qlab-utwente/Quantum-Dice-by-UTwente/images/bootAndReset.png

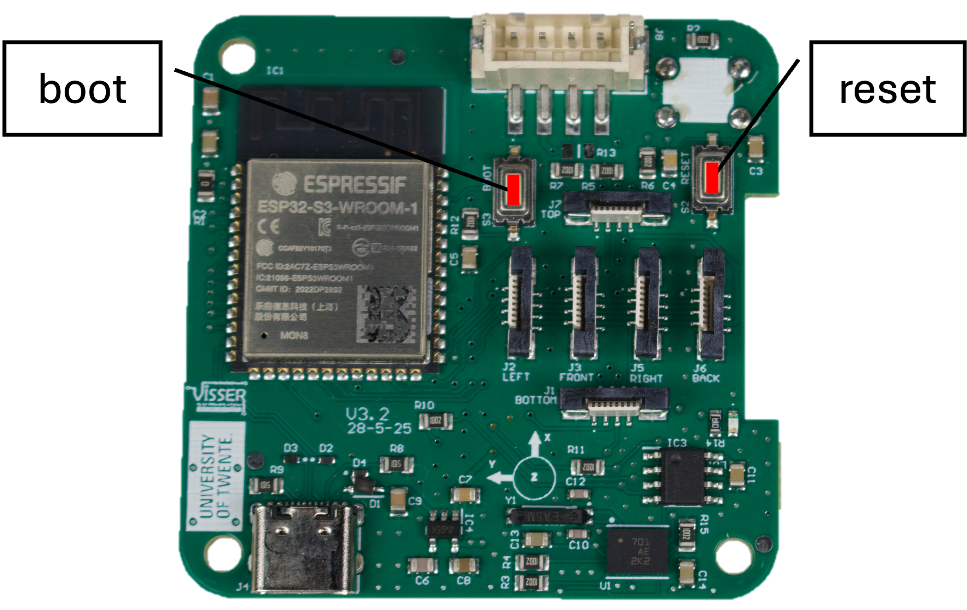
images/bootAndReset.png
