qlab-utwente/Quantum-Dice-by-UTwente/images/ESP32-S3 n16r8 arduino settings.png

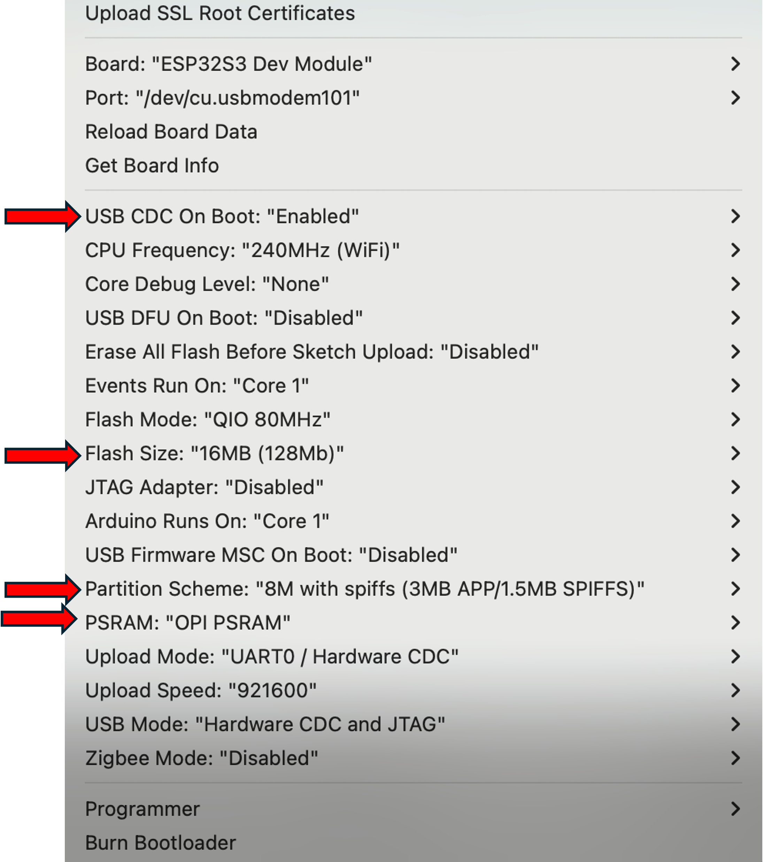
images/ESP32-S3 n16r8 arduino settings.png
