qlab-utwente/Quantum-Dice-by-UTwente/images/Exploded view Quantum Dice 2.png

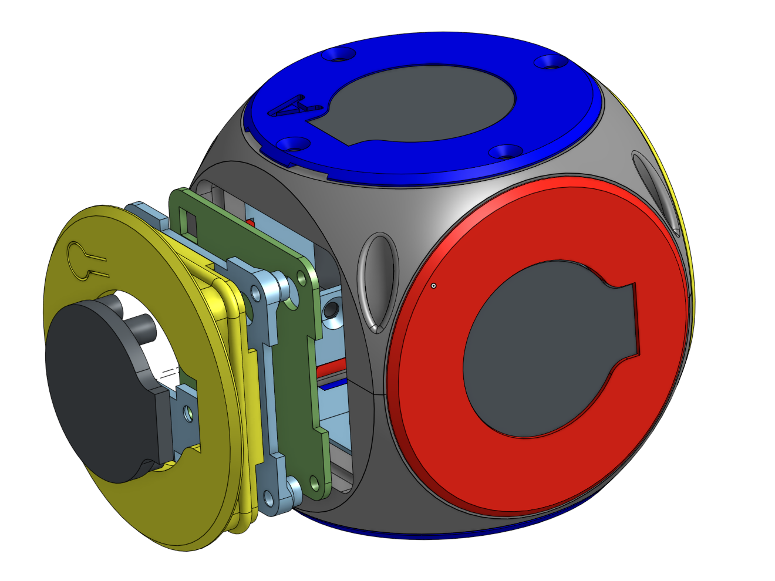
images/Exploded view Quantum Dice 2.png
