qlab-utwente/Quantum-Dice-by-UTwente/images/exploded view quantum dice.png

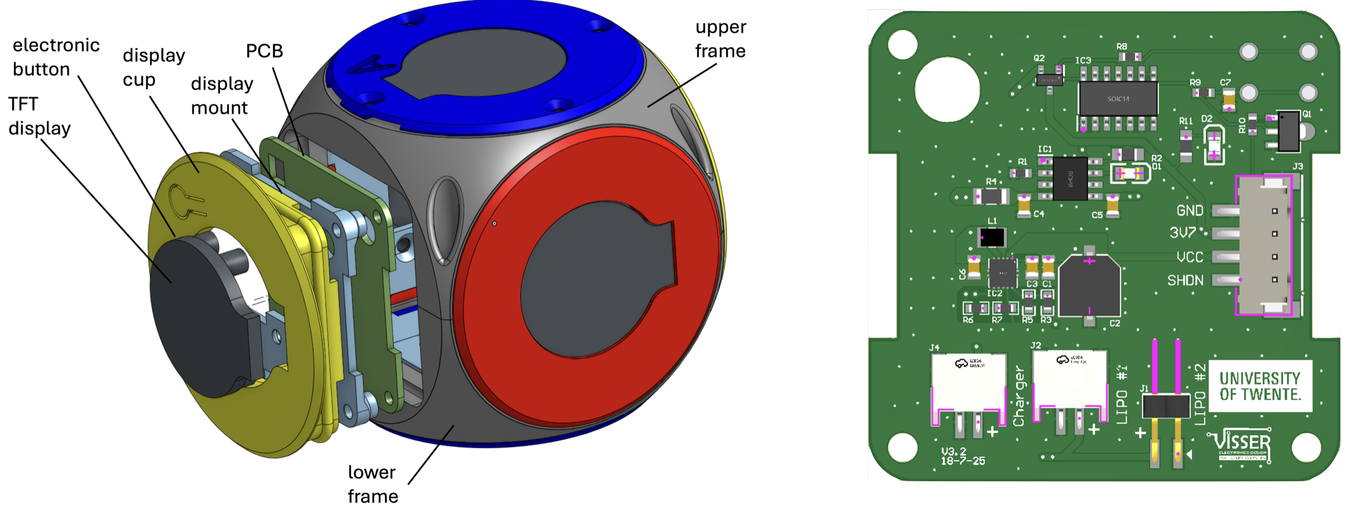
images/exploded view quantum dice.png
