qlab-utwente/Quantum-Dice-by-UTwente/images/FPC slide lock.jpg

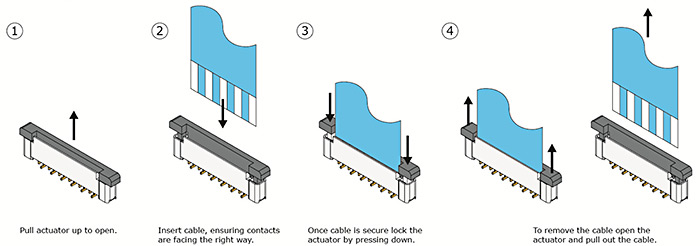
images/FPC slide lock.jpg
