qlab-utwente/Quantum-Dice-by-UTwente/images/Quantum Dice Working Principle.png

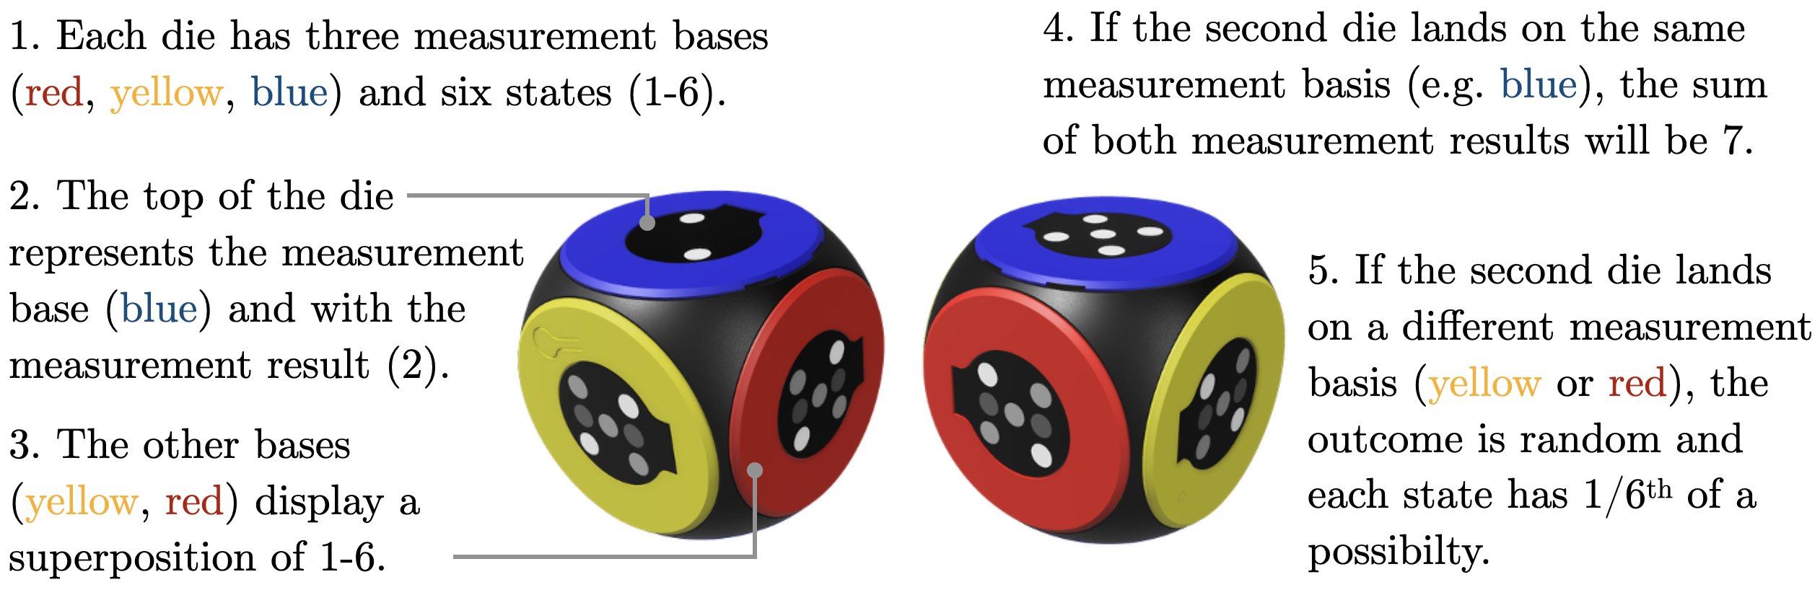
images/Quantum Dice Working Principle.png
