qlab-utwente/Quantum-Dice-by-UTwente/images/single-die-classic-to-superposition.png

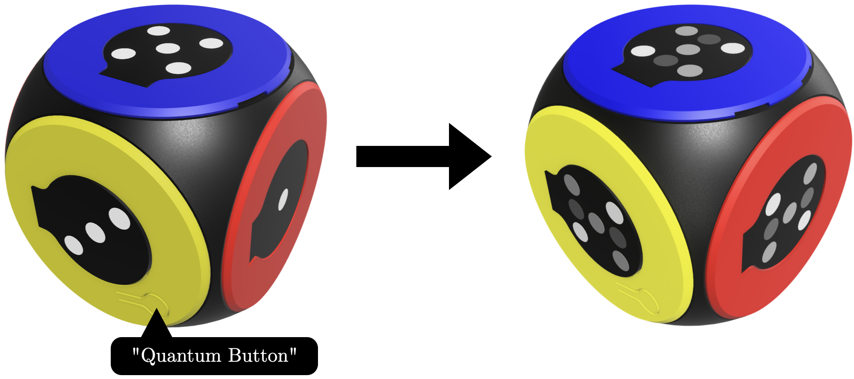
images/single-die-classic-to-superposition.png
