qlab-utwente/Quantum-Dice-by-UTwente/images/two_dice_entangled_2.png

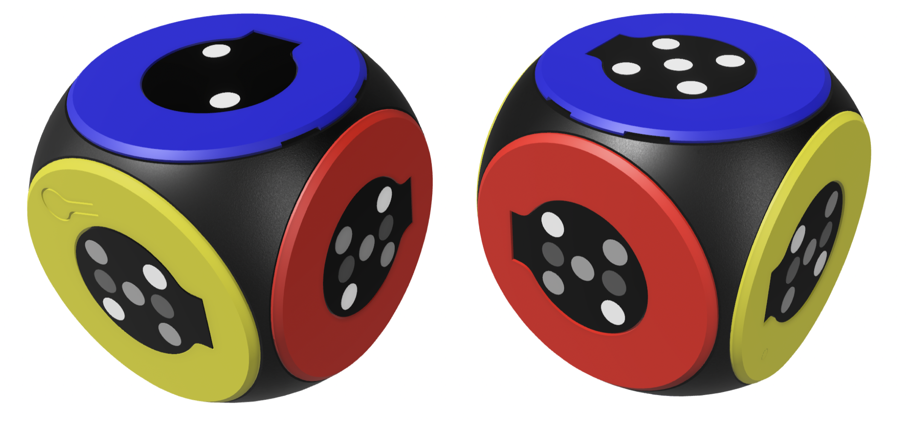
images/two_dice_entangled_2.png
