qlab-utwente/Quantum-Dice-by-UTwente/images/two_dice_entangled_3.png

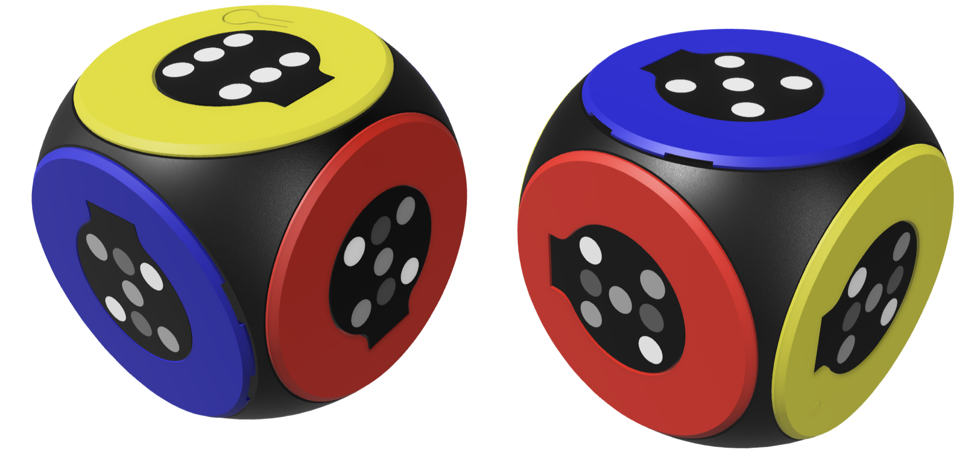
images/two_dice_entangled_3.png
