qlab-utwente/Quantum-Dice-by-UTwente/QuantumDice/IMUhelpers.cpp

#include "IMUhelpers.hpp"
#include "defines.hpp"

// ============================================
// BNO055IMUSensor IMPLEMENTATION
// ============================================

// Constructor
BNO055IMUSensor::BNO055IMUSensor() : _bno(55), _prevAccelMag(0), _currentAccelMag(0), _accelChange(0), _isMoving(false), _stableCounter(0), _currentOrientation(ORIENTATION_UNKNOWN), _motionThreshold(0.5), _stableThreshold(0.15), _stableCountRequired(10), _flatGravityMin(9.2), _flatGravityMax(10.5), _flatOtherAxisMax(3.5), _axisRemapConfig(0x06), _axisRemapSign(0x01), _xUp(0.0), _yUp(0.0), _zUp(1.0), _xUpStart(0.0), _yUpStart(0.0), _zUpStart(1.0), _prevMicros(0), _tumbleThreshold(0.707), _tumbleDetected(false), _tumbleReferenceSet(false), _firstUpdateAfterReset(false) {}

// ============================================
// CORE FUNCTIONS
// ============================================

auto BNO055IMUSensor::init() -> bool {
    // Initialize I2C and BNO055
    debug("Initializing BNO055... ");

    if (!_bno.begin()) {
        errorln("FAILED! Sensor not detected.");
        return false;  // Sensor not detected
    }

    debugln("BNO055 detected.");
    delay(100);

    // Apply custom axis remapping
    debug("Applying axis remapping... ");
    applyAxisRemap();
    debugln("done.");

    // Use external crystal for better accuracy
    _bno.setExtCrystalUse(true);

    delay(100);

    // Wait for sensor to produce sensible readings
    // This is especially important with ESP32 and I2C initialization
    debug("Waiting for stable readings... ");

    unsigned long startTime = millis();
    const unsigned long timeout = 5000;  // 5 second timeout
    bool sensibleReading = false;
    int attempts = 0;

    while (!sensibleReading && (millis() - startTime < timeout)) {
        // Read acceleration
        _accel = _bno.getVector(Adafruit_BNO055::VECTOR_ACCELEROMETER);
        _gravity = _bno.getVector(Adafruit_BNO055::VECTOR_GRAVITY);
        float mag = sqrt(_gravity.x()*_gravity.x() + _gravity.y()*_gravity.y() + _gravity.z()*_gravity.z());

        // Check if reading is sensible (close to gravity, not zero or wildly off)
        // Valid range: 7-12 m/s² (allows for some movement during init)
        if (mag > 7.0 && mag < 12.0) {
            sensibleReading = true;
            _prevAccelMag = mag;
            _currentAccelMag = mag;
            debug("OK (");
            debug(mag, 2);
            debug(" m/s² after ");
            debug(attempts);
            debugln(" attempts)");
        } else {
            attempts++;
            if (attempts % 10 == 0) {
                debug(".");
            }
            delay(50);  // Wait a bit before next reading
        }
    }

    if (!sensibleReading) {
        debugln("\nFAILED! Timeout - sensor not producing valid readings.");
        debugln("Check connections and try again.");
        return false;  // Timeout - sensor not producing valid readings
    }

    // Do a few more updates to stabilize the baseline
    debug("Stabilizing baseline... ");
    for (int i = 0; i < 5; i++) {
        _accel = _bno.getVector(Adafruit_BNO055::VECTOR_ACCELEROMETER);
        _gyro = _bno.getVector(Adafruit_BNO055::VECTOR_GYROSCOPE);
        _gravity = _bno.getVector(Adafruit_BNO055::VECTOR_GRAVITY);
        _currentAccelMag = sqrt(_accel.x()*_accel.x() + _accel.y()*_accel.y() + _accel.z()*_accel.z());
        _prevAccelMag = _currentAccelMag;
        delay(20);
    }
    debugln("done.");
    debugln("✓ BNO055 initialization complete!");

    return true;  // Success
}

void BNO055IMUSensor::update() {
    // Calculate delta time for rotation matrices
    unsigned long currentMicros = micros();
    float deltaTime = (currentMicros - _prevMicros) * 1e-6;  // Convert to seconds
    _prevMicros = currentMicros;

    // Read sensor data
    _accel = _bno.getVector(Adafruit_BNO055::VECTOR_ACCELEROMETER);
    _gravity = _bno.getVector(Adafruit_BNO055::VECTOR_GRAVITY);
    _gyro = _bno.getVector(Adafruit_BNO055::VECTOR_GYROSCOPE);

    // Calculate acceleration magnitude
    _currentAccelMag = sqrt(_accel.x()*_accel.x() + _accel.y()*_accel.y() + _accel.z()*_accel.z());
    float _gyroMag = sqrt(_gyro.x()*_gyro.x() + _gyro.y()*_gyro.y() + _gyro.z()*_gyro.z());

    // Motion detection logic
    if (_gyroMag > _motionThreshold) {
        // Significant change = motion detected
        _isMoving = true;
        _stableCounter = 0;
    }
    else if (_gyroMag < _stableThreshold) {
        // Very little change = potentially stable
        _stableCounter++;

        if (_isMoving && _stableCounter >= _stableCountRequired) {
            // Been stable long enough
            _isMoving = false;
        }
    }
    else {
        // In between - small movements
        if (_stableCounter > 0) {
            _stableCounter--;  // Slowly decay stable counter
        }
    }

    // Detect orientation
    _currentOrientation = detectOrientation();

    // Update up vector using rotation matrices (if reference is set)
    if (_tumbleReferenceSet) {
        // Skip first update after reset to avoid bad deltaTime
        if (_firstUpdateAfterReset) {
            _firstUpdateAfterReset = false;
            _prevMicros = currentMicros;  // Reset timing
        }
        else if (deltaTime > 0.0 && deltaTime < 1.0) {
            updateUpVector(deltaTime);

            // Check for tumble by comparing current up vector with initial reference
            float dotProduct = (_xUp * _xUpStart) + (_yUp * _yUpStart) + (_zUp * _zUpStart);

            // Clamp to valid range for acos
            dotProduct = constrain(dotProduct, -1.0, 1.0);

            // Check if tumbled beyond threshold
            if (dotProduct < _tumbleThreshold) {
                _tumbleDetected = true;
            }
        }
    }

    // Update previous magnitude for next iteration
    _prevAccelMag = _currentAccelMag;
}

// ============================================
// MOTION DETECTION
// ============================================

auto BNO055IMUSensor::moving() -> bool {
    return _isMoving;
}

auto BNO055IMUSensor::stable() -> bool {
    return !_isMoving && (_stableCounter >= _stableCountRequired);
}

// ============================================
// ORIENTATION DETECTION
// ============================================

auto BNO055IMUSensor::on_table() -> bool {
    // Check if orientation is one of the flat positions (not tilted or unknown)
    return (_currentOrientation != ORIENTATION_UNKNOWN &&
            _currentOrientation != ORIENTATION_TILTED);
}

auto BNO055IMUSensor::orientation() -> IMU_Orientation {
    return _currentOrientation;
}

auto BNO055IMUSensor::getOrientationString() -> String {
    switch (_currentOrientation) {
        case ORIENTATION_Z_UP:
            return "Z+ UP (Vertical - Normal)";
        case ORIENTATION_Z_DOWN:
            return "Z- UP (Vertical - Inverted)";
        case ORIENTATION_X_UP:
            return "X+ UP";
        case ORIENTATION_X_DOWN:
            return "X- UP";
        case ORIENTATION_Y_UP:
            return "Y+ UP";
        case ORIENTATION_Y_DOWN:
            return "Y- UP";
        case ORIENTATION_TILTED:
            return "TILTED (not aligned)";
        default:
            return "UNKNOWN";
    }
}

// ============================================
// GYROSCOPE
// ============================================

auto BNO055IMUSensor::gyroX() -> float {
    return _gyro.x();
}

auto BNO055IMUSensor::gyroY() -> float {
    return _gyro.y();
}

auto BNO055IMUSensor::gyroZ() -> float {
    return _gyro.z();
}

// ============================================
// ACCELEROMETER
// ============================================

auto BNO055IMUSensor::accelX() -> float {
    return _accel.x();
}

auto BNO055IMUSensor::accelY() -> float {
    return _accel.y();
}

auto BNO055IMUSensor::accelZ() -> float {
    return _accel.z();
}

auto BNO055IMUSensor::getAccelMagnitude() -> float {
    return _currentAccelMag;
}

auto BNO055IMUSensor::getAccelChange() -> float {
    return _accelChange;
}

// ============================================
// GRAVITY
// ===========================================

auto BNO055IMUSensor::getGravityX() -> float {
    return _gravity.x();
}

auto BNO055IMUSensor::getGravityY() -> float {
    return _gravity.y();
}

auto BNO055IMUSensor::getGravityZ() -> float {
    return _gravity.z();
}

// ============================================
// CALIBRATION
// ============================================

void BNO055IMUSensor::getCalibration(uint8_t* system, uint8_t* gyro, uint8_t* accel, uint8_t* mag) {
    _bno.getCalibration(system, gyro, accel, mag);
}

auto BNO055IMUSensor::isCalibrated() -> bool {
    uint8_t system = 0;
    uint8_t gyro = 0;
    uint8_t accel = 0;
    uint8_t mag = 0;
    _bno.getCalibration(&system, &gyro, &accel, &mag);
    return (system >= 2 && gyro >= 2 && accel >= 2 && mag >= 2);
}

// ============================================
// TUMBLE DETECTION
// ============================================

void BNO055IMUSensor::resetTumbleDetection() {
    // Get current acceleration (gravity) vector
    _gravity = _bno.getVector(Adafruit_BNO055::VECTOR_GRAVITY);

    // Calculate magnitude
    float mag = sqrt(_gravity.x()*_gravity.x() + _gravity.y()*_gravity.y() + _gravity.z()*_gravity.z());

    // Normalize to unit vector (invert because gravity points down, we want "up")
    // Avoid division by zero
    if (mag > 0.1) {
        _xUpStart = -_gravity.x() / mag;
        _yUpStart = -_gravity.y() / mag;
        _zUpStart = -_gravity.z() / mag;

        // Initialize current up vector to same as start
        _xUp = _xUpStart;
        _yUp = _yUpStart;
        _zUp = _zUpStart;

        // Reset timing
        _prevMicros = micros();

        // Clear detection flags
        _tumbleDetected = false;
        _tumbleReferenceSet = true;
        _firstUpdateAfterReset = true;  // Skip first update to avoid bad deltaTime
    }
}

auto BNO055IMUSensor::tumbled() -> bool {
    return _tumbleDetected;
}

auto BNO055IMUSensor::getTumbleAngle() -> float {
    if (!_tumbleReferenceSet) {
        return 0.0;  // No reference set
    }

    // Calculate dot product between current and initial up vectors
    float dotProduct = (_xUp * _xUpStart) + (_yUp * _yUpStart) + (_zUp * _zUpStart);

    // Clamp to valid range for acos
    dotProduct = constrain(dotProduct, -1.0, 1.0);

    // Convert to angle in degrees
    double angleRadians = acos(dotProduct);
    double angleDegrees = angleRadians * 57.2958;  // 180/PI

    return (float) angleDegrees;
}

// ============================================
// CONFIGURATION & TUNING
// ============================================

void BNO055IMUSensor::setMotionThreshold(float threshold) {
    _motionThreshold = threshold;
}

void BNO055IMUSensor::setStableThreshold(float threshold) {
    _stableThreshold = threshold;
}

void BNO055IMUSensor::setStableCount(int count) {
    _stableCountRequired = count;
}

void BNO055IMUSensor::setTumbleThreshold(float threshold) {
    _tumbleThreshold = threshold;  // Threshold is cosine of angle
                                   // Reset tumble detection when threshold changes
    _tumbleDetected = false;
}

void BNO055IMUSensor::setOrientationThresholds(float minGravity, float maxGravity, float maxOtherAxis) {
    _flatGravityMin = minGravity;
    _flatGravityMax = maxGravity;
    _flatOtherAxisMax = maxOtherAxis;
}

// ============================================
// AXIS REMAPPING
// ============================================

void BNO055IMUSensor::setAxisRemap(uint8_t config, uint8_t sign) {
    _axisRemapConfig = config;
    _axisRemapSign = sign;
    applyAxisRemap();
}

void BNO055IMUSensor::getAxisRemap(uint8_t* config, uint8_t* sign) {
    *config = readRegister(BNO055_AXIS_MAP_CONFIG_ADDR);
    *sign = readRegister(BNO055_AXIS_MAP_SIGN_ADDR);
}

// ============================================
// PRIVATE HELPER FUNCTIONS
// ============================================

auto BNO055IMUSensor::detectOrientation() -> IMU_Orientation {
    float x = _gravity.x();
    float y = _gravity.y();
    float z = _gravity.z();

    // Note: Accelerometer reads NEGATIVE when axis points UP (gravity pulls down)
    // and POSITIVE when axis points DOWN (accelerating toward ground)

    // Check which axis is aligned with gravity
    bool xDown = (abs(x) > _flatGravityMin && abs(x) < _flatGravityMax);
    bool yDown = (abs(y) > _flatGravityMin && abs(y) < _flatGravityMax);
    bool zDown = (abs(z) > _flatGravityMin && abs(z) < _flatGravityMax);

    // Z-axis aligned (physical X+ up = normal vertical)
    if (zDown && abs(x) < _flatOtherAxisMax && abs(y) < _flatOtherAxisMax) {
        return (z < 0) ? ORIENTATION_Z_UP : ORIENTATION_Z_DOWN;
    }

    // X-axis aligned (tilted toward physical Z direction)
    if (xDown && abs(y) < _flatOtherAxisMax && abs(z) < _flatOtherAxisMax) {
        return (x < 0) ? ORIENTATION_X_UP : ORIENTATION_X_DOWN;
    }

    // Y-axis aligned (tilted sideways)
    if (yDown && abs(x) < _flatOtherAxisMax && abs(z) < _flatOtherAxisMax) {
        return (y < 0) ? ORIENTATION_Y_UP : ORIENTATION_Y_DOWN;
    }

    // Not aligned with any axis
    return ORIENTATION_TILTED;
}

void BNO055IMUSensor::applyAxisRemap() {
    // Must be in CONFIG mode to change axis remap
    writeRegister(BNO055_OPR_MODE_ADDR, 0x00);
    delay(25);

    // Write custom axis remap configuration
    writeRegister(BNO055_AXIS_MAP_CONFIG_ADDR, _axisRemapConfig);
    delay(10);

    // Write custom axis sign configuration
    writeRegister(BNO055_AXIS_MAP_SIGN_ADDR, _axisRemapSign);
    delay(10);

    // Switch to NDOF mode (all sensors + fusion)
    writeRegister(BNO055_OPR_MODE_ADDR, 0x0C);
    delay(25);
}

auto BNO055IMUSensor::readRegister(uint8_t reg) -> uint8_t {
    uint8_t value = 0;
    Wire.beginTransmission(BNO055_ADDRESS_A);
    Wire.write(reg);
    Wire.endTransmission();
    Wire.requestFrom(BNO055_ADDRESS_A, (uint8_t)1);
    value = Wire.read();
    return value;
}

void BNO055IMUSensor::writeRegister(uint8_t reg, uint8_t value) {
    Wire.beginTransmission(BNO055_ADDRESS_A);
    Wire.write(reg);
    Wire.write(value);
    Wire.endTransmission();
    delay(2);
}

// ============================================
// TUMBLE DETECTION - ROTATION MATRIX UPDATE
// ============================================

void BNO055IMUSensor::updateUpVector(float deltaTime) {
    // BNO055 outputs gyroscope in DEGREES per second, not radians!
    // Convert to radians per second, then calculate rotation angles

    float xRot = _gyro.x() * DEG_TO_RAD * deltaTime;
    float yRot = _gyro.y() * DEG_TO_RAD * deltaTime;
    float zRot = _gyro.z() * DEG_TO_RAD * deltaTime;

    // Apply rotation matrices sequentially: X, then Y, then Z
    // This updates the current "up" vector based on the rotation

    // X-axis rotation matrix
    // Rotates around X-axis, affects Y and Z components
    float xUp = _xUp;
    float yUp = (_yUp * cos(xRot)) - (_zUp * sin(xRot));
    float zUp = (_yUp * sin(xRot)) + (_zUp * cos(xRot));

    _xUp = xUp;
    _yUp = yUp;
    _zUp = zUp;

    // Y-axis rotation matrix
    // Rotates around Y-axis, affects X and Z components
    xUp = (_xUp * cos(yRot)) + (_zUp * sin(yRot));
    yUp = _yUp;
    zUp = (-_xUp * sin(yRot)) + (_zUp * cos(yRot));

    _xUp = xUp;
    _yUp = yUp;
    _zUp = zUp;

    // Z-axis rotation matrix
    // Rotates around Z-axis, affects X and Y components
    xUp = (_xUp * cos(zRot)) - (_yUp * sin(zRot));
    yUp = (_xUp * sin(zRot)) + (_yUp * cos(zRot));
    zUp = _zUp;

    _xUp = xUp;
    _yUp = yUp;
    _zUp = zUp;

    // Calculate magnitude before normalization
    float magnitude = sqrt((_xUp * _xUp) + (_yUp * _yUp) + (_zUp * _zUp));

    // CRITICAL: Renormalize the up vector to prevent drift
    // Floating-point errors accumulate, causing magnitude to drift from 1.0
    // This would make dot product calculations unreliable
    if (magnitude > 0.01) {  // Avoid division by zero
        _xUp /= magnitude;
        _yUp /= magnitude;
        _zUp /= magnitude;
    }
}

// ============================================
// DEBUG FUNCTIONS
// ============================================

auto BNO055IMUSensor::getDebugDotProduct() -> float {
    if (!_tumbleReferenceSet) {
        return 1.0;  // No reference set, return 1.0
    }

    float dotProduct = (_xUp * _xUpStart) + (_yUp * _yUpStart) + (_zUp * _zUpStart);
    return constrain(dotProduct, -1.0, 1.0);
}

void BNO055IMUSensor::getDebugUpVector(float* x, float* y, float* z) {
    *x = _xUp;
    *y = _yUp;
    *z = _zUp;
}

void BNO055IMUSensor::getDebugUpStart(float* x, float* y, float* z) {
    *x = _xUpStart;
    *y = _yUpStart;
    *z = _zUpStart;
}

void BNO055IMUSensor::printDebugInfo() {
    info("UpStart:(");
    info(_xUpStart, 4);
    info(", ");
    info(_yUpStart, 4);
    info(", ");
    info(_zUpStart, 4);
    info(") | Up:(");
    info(_xUp, 4);
    info(", ");
    info(_yUp, 4);
    info(", ");
    info(_zUp, 4);
    info(") | Gyro:(");
    info(_gyro.x(), 4);
    info(", ");
    info(_gyro.y(), 4);
    info(", ");
    info(_gyro.z(), 4);
    info(") | Dot:");
    info(getDebugDotProduct(), 4);
    info(" | Angle:");
    info(getTumbleAngle(), 2);
    infoln("°");
}
