qlab-utwente/Quantum-Dice-by-UTwente/QuantumDice/handyHelpers.hpp

#ifndef HANDYHELPERS_H_
#define HANDYHELPERS_H_

#include "IMUhelpers.hpp"
#include <Button2.h>
#include <cstdint>

// Hardware pin assignments structure
struct HardwarePins {
    // TFT Display pins
    uint8_t tft_cs;
    uint8_t tft_rst;
    uint8_t tft_dc;

    // Screen CS pins (6 screens)
    uint8_t screen_cs[6];

    // Screen address mapping for SMD/HDR
    uint8_t screenAddress[16];

    // ADC pin for battery monitoring
    uint8_t adc_pin;
};

// Global configuration and hardware objects
extern HardwarePins hwPins;

// Hardware initialization
void initHardwarePins();
void printHardwarePins();

// Existing declarations
extern RTC_DATA_ATTR int bootCount;
extern Button2           button;
extern bool              clicked;
extern bool              longclicked;

void initButton();
void longClickDetected(Button2 &btn);
void click(Button2 &btn);
void checkTimeForDeepSleep(IMUSensor *imuSensor);
auto checkMinimumVoltage() -> bool;
auto mapFloat(float x, float in_min, float in_max, float out_min, float out_max, bool clipOutput) -> float;
auto withinBounds(float val, float minimum, float maximum) -> bool;
void initSerial();
auto generateDiceRollRejection() -> uint8_t;
auto generateDiceRoll() -> uint8_t;

#endif /* HANDYHELPERS_H_ */
