qlab-utwente/Quantum-Dice-by-UTwente/example_configs/DEV1_config.txt

# Dice Configuration File
# Lines starting with # are comments
# Edit values after the = sign
# Save this file as XXXXX_config.txt (XXXXX is diceID) maximum of 5 characters
# upload to your Quantum Dice (See instructions)
# https://thelastoutpostworkshop.github.io/ESPConnect/

# ==========================================
# DEVICE IDENTIFICATION (UNIQUE)
# ==========================================
# Unique identifier for this dice (max 5 characters)
diceId=DEV1

# Below's setting is for Advanced users. Default values are ok to use

# ==========================================
# DISPLAY COLORS
# ==========================================
# 16-bit RGB565 format (0-65535)
# Common colors:
#   Red:    63488 (0xF800)
#   Green:  2016  (0x07E0)
#   Blue:   31    (0x001F)
#   White:  65535 (0xFFFF)
#   Black:  0     (0x0000)
#   Yellow: 65504 (0xFFE0)
#   Cyan:   2047  (0x07FF)
#   Magenta:63519 (0xF81F)

x_background=0        	  # Black
y_background=0            # Black
z_background=0            # Black

# Entanglement colors (16-bit RGB565 format)
# This dice will randomly pick from these colors when accepting an entanglement request
# You can add multiple colors separated by commas
# Examples: Yellow=65504, Green=2016, Cyan=2047, Magenta=63519, Red=63488, Blue=31
entang_colors=65504,2016,2047,63519

# Color flash timeout (milliseconds)
# Duration to show actual color when receiving entanglement (if showColors is OFF)
colorFlashTimeout=250

# ==========================================
# RSSI SETTINGS
# ==========================================
# Signal strength threshold for entanglement detection
# Typical values: -40 (very close) to -80 (far)
# More negative = weaker signal allowed
rssiLimit=-35

# ==========================================
# HARDWARE CONFIGURATION
# ==========================================
# Settings to accomodate legacy boards
# Set to true or false (or 1/0)
isSMD=true           # true for SMD components, false for HDR
isNano=false         # true for NANO board, false for DEVKIT

# ==========================================
# OPERATIONAL PARAMETERS
# ==========================================
# Deep sleep timeout (milliseconds)
# Time of inactivity before entering deep sleep
# 300000 = 5 minutes, 600000 = 10 minutes
deepSleepTimeout=300000

# ==========================================
# CHECKSUM
# ==========================================
# Auto-calculated when saving from ESP32
# Set to 0 to disable validation
checksum=0
